tonazza/TonazWeatherStation/software/MS5805_02BA01.py

# Distributed with a free-will license.
# Use it any way you want, profit or free, provided it fits in the licenses of its associated works.
# MS5805_02BA01
# This code is designed to work with the MS5805_02BA01_I2CADC I2C Mini Module available from ControlEverything.com.
# https://www.controleverything.com/products

import smbus
import time

# Get I2C bus
bus = smbus.SMBus(1)

# MS5805_02BA01 address, 0x76(118)
#		0x1E(30)	Reset command
bus.write_byte(0x76, 0x1E)

time.sleep(0.3)

# Read 12 bytes of calibration data
# Read pressure sensitivity
data = bus.read_i2c_block_data(0x76, 0xA2, 2)
C1 = data[0] * 256 + data[1]

# Read pressure offset
data = bus.read_i2c_block_data(0x76, 0xA4, 2)
C2 = data[0] * 256 + data[1]

# Read temperature coefficient of pressure sensitivity
data = bus.read_i2c_block_data(0x76, 0xA6, 2)
C3 = data[0] * 256 + data[1]

# Read temperature coefficient of pressure offset
data = bus.read_i2c_block_data(0x76, 0xA8, 2)
C4 = data[0] * 256 + data[1]

# Read reference temperature
data = bus.read_i2c_block_data(0x76, 0xAA, 2)
C5 = data[0] * 256 + data[1]

# Read temperature coefficient of the temperature
data = bus.read_i2c_block_data(0x76, 0xAC, 2)
C6 = data[0] * 256 + data[1]

# MS5805_02BA01 address, 0x76(118)
#		0x40(64)	Pressure conversion(OSR = 256) command
bus.write_byte(0x76, 0x40)

time.sleep(0.5)

# Read digital pressure value
# Read data back from 0x00(0), 3 bytes
# D1 MSB2, D1 MSB1, D1 LSB
value = bus.read_i2c_block_data(0x76, 0x00, 3)
D1 = value[0] * 65536 + value[1] * 256 + value[2]

# MS5805_02BA01 address, 0x76(118)
#		0x50(64)	Temperature conversion(OSR = 256) command
bus.write_byte(0x76, 0x50)

time.sleep(0.5)

# Read digital temperature value
# Read data back from 0x00(0), 3 bytes
# D2 MSB2, D2 MSB1, D2 LSB
value = bus.read_i2c_block_data(0x76, 0x00, 3)
D2 = value[0] * 65536 + value[1] * 256 + value[2]

dT = D2 - C5 * 256
TEMP = 2000 + dT * C6 / 8388608
OFF = C2 * 131072 + (C4 * dT) / 64
SENS = C1 * 65536 + (C3 * dT ) / 128
T2 = 0
OFF2 = 0
SENS2 = 0

if TEMP < 2000 :
	T2 = 11 *(dT * dT) / 34359738368
	OFF2 = 31 * ((TEMP - 2000) * (TEMP - 2000)) / 8
	SENS2 = 63 * ((TEMP - 2000) * (TEMP - 2000)) / 32

TEMP2 = TEMP - T2
OFF2 = OFF - OFF2
SENS2 = SENS - SENS2
pressure = (((((D1 * SENS2) / 2097152) - OFF2) / 32768)) / 100.0
cTemp = TEMP2 / 100.0
fTemp = cTemp * 1.8 + 32

# Output data to screen
print ("Pressure : %.2f mbar" %pressure)
print ("Temperature in Celsius : %.2f C" %cTemp)
print ("Temperature in Fahrenheit : %.2f F" %fTemp)
